h0lad/PicoLoRaHarvester/src/LoRaWAN/App/lora_app.c

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

/* Includes ------------------------------------------------------------------*/
#include "platform.h"
#include "sys_app.h"
#include "lora_app.h"
#include "stm32_seq.h"
#include "stm32_timer.h"
#include "utilities_def.h"
#include "app_version.h"
#include "Commissioning.h"
#include "subghz_phy_version.h"
#include "smtc_modem_api.h"
#include "smtc_modem_utilities.h"
#include "smtc_modem_hal.h"
#include "smtc_modem_relay_api.h"
#include "adc_if.h"
#include "CayenneLpp.h"
#include "sys_sensors.h"
#include "flash_if.h"
#include "rng.h"
#include "lorawan_api.h"
#include "stm32_lpm.h"

/* USER CODE BEGIN Includes */
#include "telemetry.h"
#include <stdlib.h>
/* USER CODE END Includes */

/* External variables ---------------------------------------------------------*/
/**
  * @brief LoRa State Machine states
  */
typedef enum TxEventType_e
{
  /**
    * @brief Appdata Transmission issue based on timer every TxDutyCycleTime
    */
  TX_ON_TIMER,
  /**
    * @brief Appdata Transmission external event plugged on OnSendEvent( )
    */
  TX_ON_EVENT
} TxEventType_t;

/**
  * LEDs period value of the timer in ms
  */
#define LED_PERIOD_TIME 500

/**
  * Join switch period value of the timer in ms
  */
#define JOIN_TIME 2000

/**
  * Uplink time interval in Certification mode is 10s (recommended value)
  */
#define CERT_TX_DUTYCYCLE   10

/**
  * Stack id value (multistacks modem is not yet available)
  */
#define STACK_ID 0

/*---------------------------------------------------------------------------*/
/*                             LoRaWAN NVM configuration                     */
/*---------------------------------------------------------------------------*/
/**
  * @brief LoRaWAN NVM Flash address
  * @note last 2 sector of a 256kBytes device
  */
#define LORAWAN_NVM_BASE_ADDRESS        (0x0803F000UL)

#define SECURE_ELEMENT_CONTEXT_SIZE     0x2A0UL
#define MODEM_CONTEXT_SIZE              0x10UL
#define LORAWAN_CONTEXT_SIZE            0x28UL

#define ADDR_FLASH_LORAWAN_CONTEXT              LORAWAN_NVM_BASE_ADDRESS
#define ADDR_FLASH_MODEM_CONTEXT                (void *)(LORAWAN_NVM_BASE_ADDRESS + LORAWAN_CONTEXT_SIZE)
#define ADDR_FLASH_SECURE_ELEMENT_CONTEXT       (void *)(LORAWAN_NVM_BASE_ADDRESS + LORAWAN_CONTEXT_SIZE + MODEM_CONTEXT_SIZE)

/* USER CODE BEGIN PD */
#define TTN_MAX_DAILY_AIRTIME_S       30UL
#define SECONDS_PER_DAY               86400UL
#define TTN_AIRTIME_USAGE_PCT         100UL
#define TX_INTERVAL_MIN_S             60UL
#define LORAWAN_MAC_OVERHEAD_BYTES    13UL
#define DOWNLINK_CMD_UPLINK           0x01U
#define DOWNLINK_CMD_RESET            0x02U
/* USER CODE END PD */


/*!
 * @brief Stringify constants
 */
#define xstr( a ) str( a )
#define str( a ) #a

/*!
 * @brief Helper macro that returned a human-friendly message if a command does not return SMTC_MODEM_RC_OK
 *
 * @remark The macro is implemented to be used with functions returning a @ref smtc_modem_return_code_t
 *
 * @param[in] rc  Return code
 */

#define ASSERT_SMTC_MODEM_RC( rc_func )                                                     \
  do                                                                                        \
  {                                                                                         \
    smtc_modem_return_code_t rc = rc_func;                                                  \
    if( rc == SMTC_MODEM_RC_NOT_INIT )                                                      \
    {                                                                                       \
      APP_LOG(TS_OFF, VLEVEL_H,  "In %s - %s (line %d): %s\r\n", __FILE__, __func__, __LINE__,   \
              xstr( SMTC_MODEM_RC_NOT_INIT ) );                             \
    }                                                                                       \
    else if( rc == SMTC_MODEM_RC_INVALID )                                                  \
    {                                                                                       \
      APP_LOG(TS_OFF, VLEVEL_H,  "In %s - %s (line %d): %s\r\n", __FILE__, __func__, __LINE__,   \
              xstr( SMTC_MODEM_RC_INVALID ) );                              \
    }                                                                                       \
    else if( rc == SMTC_MODEM_RC_BUSY )                                                     \
    {                                                                                       \
      APP_LOG(TS_OFF, VLEVEL_H,  "In %s - %s (line %d): %s\r\n", __FILE__, __func__, __LINE__,   \
              xstr( SMTC_MODEM_RC_BUSY ) );                                 \
    }                                                                                       \
    else if( rc == SMTC_MODEM_RC_FAIL )                                                     \
    {                                                                                       \
      APP_LOG(TS_OFF, VLEVEL_H,  "In %s - %s (line %d): %s\r\n", __FILE__, __func__, __LINE__,   \
              xstr( SMTC_MODEM_RC_FAIL ) );                                 \
    }                                                                                       \
    else if( rc == SMTC_MODEM_RC_NO_TIME )                                                  \
    {                                                                                       \
      APP_LOG(TS_OFF, VLEVEL_L,  "In %s - %s (line %d): %s\r\n", __FILE__, __func__, __LINE__, \
              xstr( SMTC_MODEM_RC_NO_TIME ) );                            \
    }                                                                                       \
    else if( rc == SMTC_MODEM_RC_INVALID_STACK_ID )                                         \
    {                                                                                       \
      APP_LOG(TS_OFF, VLEVEL_H,  "In %s - %s (line %d): %s\r\n", __FILE__, __func__, __LINE__,   \
              xstr( SMTC_MODEM_RC_INVALID_STACK_ID ) );                     \
    }                                                                                       \
    else if( rc == SMTC_MODEM_RC_NO_EVENT )                                                 \
    {                                                                                       \
      APP_LOG(TS_OFF, VLEVEL_M,  "In %s - %s (line %d): %s\r\n", __FILE__, __func__, __LINE__,    \
              xstr( SMTC_MODEM_RC_NO_EVENT ) );                              \
    }                                                                                       \
  } while( 0 )


/**
  * @brief  LoRa End Node send request
  */
static void SendTxData(uint8_t port);
#if defined (LOW_POWER_DISABLE) && (LOW_POWER_DISABLE == 0)
/**
  * @brief  Sleep timer callback function
  * @param  context ptr
  */
static void OnSleepTimerEvent(void *context);
#endif /* (LOW_POWER_DISABLE) && (LOW_POWER_DISABLE == 0) */

/**
  * @brief User callback for event
  *
  *  This callback is called every time an event ( see smtc_modem_event_t ) appears in the modem.
  *  Several events may have to be read from the modem when this callback is called.
  */
static void EventCallback(void);

/*!
 * Restore the NVM Data context from the Flash
 *
* @param [in]  ctx_type   Type of modem context that need to be restored
* @param [in]  offset     Memory offset after ctx_type address
* @param [out] buffer     Buffer pointer to write to
* @param [in]  size       Buffer size to read in bytes
*/
static void RestoreContext(const modem_context_type_t ctx_type, uint32_t offset, uint8_t *buffer, const uint32_t size);
/*!
 * Store the NVM Data context to the Flash
 *
* @param [in] ctx_type   Type of modem context that need to be saved
* @param [in] offset     Memory offset after ctx_type address
* @param [in] buffer     Buffer pointer to write from
* @param [in] size       Buffer size to write in bytes
*/
static void StoreContext(const modem_context_type_t ctx_type, uint32_t offset, const uint8_t *buffer,
                         const uint32_t size);
/*!
 * Get Random value using the RNG module
 *
 * \retval value  Return the random value
 */
static uint32_t GetRandomValue(void);

/*!
 * Will be called to reset the system
 * \note Compliance test protocol callbacks used when TS001-1.0.4 + TS009 1.0.0 are defined
 */
static void SystemReset(void);

/* USER CODE BEGIN PFP */
static uint32_t compute_toa_ms(uint8_t dr, uint8_t payload_len);
static uint32_t compute_tx_interval_s(uint8_t dr);
/* USER CODE END PFP */


/**
  * @brief LoRaWAN User credentials
  */
static uint8_t user_dev_eui[8]      = FORMAT32_KEY(LORAWAN_DEVICE_EUI);
static uint8_t user_join_eui[8]     = FORMAT32_KEY(LORAWAN_JOIN_EUI);
static uint8_t user_gen_app_key[16] = FORMAT_KEY(LORAWAN_GEN_APP_KEY);
static uint8_t user_app_key[16]     = FORMAT_KEY(LORAWAN_APP_KEY);
/**
  * @brief  Buffer for rx payload
  */
static uint8_t                  rx_payload[SMTC_MODEM_MAX_LORAWAN_PAYLOAD_LENGTH] = { 0 };

/**
  * @brief  Size of the payload in the rx_payload buffer
  */
static uint8_t                  rx_payload_size = 0;

/**
  * @brief  Metadata of downlink
  */
static smtc_modem_dl_metadata_t rx_metadata     = { 0 };

/**
  * @brief  Remaining downlink payload in modem
  */
static uint8_t                  rx_remaining    = 0;

/**
  * @brief  Flag for button status
  */
static volatile bool user_button_is_press = false;

/**
  * @brief LoRaWAN Certification Mode
  */
static bool CertMode = LORAWAN_CERTIFICATION_MODE;

/**
  * @brief Type of Event to generate application Tx
  */
static TxEventType_t EventType = TX_ON_TIMER;

#if defined (LOW_POWER_DISABLE) && (LOW_POWER_DISABLE == 0)
/**
  * @brief Timer to handle the sleep time
  */
static UTIL_TIMER_Object_t SleepTimer;
#endif /* (LOW_POWER_DISABLE) && (LOW_POWER_DISABLE == 0) */

/**
  * Temp buffer to store a FLASH page in RAM when partial replacement is needed
  */
static uint8_t FLASH_RAM_buffer[FLASH_IF_BUFFER_SIZE];

/**
  * @brief Handler Callbacks
  */
static Callbacks_t Callbacks =
{
  .EventCallback =                EventCallback,
  .RestoreContext =               RestoreContext,
  .StoreContext =                 StoreContext,
  .GetRandomValue =               GetRandomValue,
  .GetBatteryLevel =              GetBatteryLevel,
  .GetTemperatureLevel =          GetTemperatureLevel,
  .SystemReset =                  SystemReset,
};

/* USER CODE BEGIN PV */
/**
  * @brief User application payload buffer
  */
static uint8_t AppDataBuffer[LORAWAN_APP_DATA_BUFFER_MAX_SIZE];
/* USER CODE END PV */

/* Exported functions ---------------------------------------------------------*/
/*
 * -----------------------------------------------------------------------------
 * --- PUBLIC FUNCTIONS DEFINITION ---------------------------------------------
 */

void LoRaWAN_Init(void)
{
  /* USER CODE BEGIN LoRaWAN_Init_1 */
  telemetry_init();
  /* USER CODE END LoRaWAN_Init_1 */

  if (FLASH_IF_Init(FLASH_RAM_buffer) != FLASH_IF_OK)
  {
    Error_Handler();
  }

#if defined (LOW_POWER_DISABLE) && (LOW_POWER_DISABLE == 0)
  UTIL_TIMER_Create(&SleepTimer, LED_PERIOD_TIME, UTIL_TIMER_ONESHOT, OnSleepTimerEvent, NULL);
#endif /* (LOW_POWER_DISABLE) && (LOW_POWER_DISABLE == 0) */
  /* Init the Lora Stack*/
  /* Init the modem and use EventCallback as event callback, please note that the callback will be */
  /* called immediately after the first call to smtc_modem_run_engine because of the reset detection */
  smtc_modem_init(&Callbacks);

  /* Certification mode is disabled by default. It can be enabled setting LORAWAN_CERTIFICATION_MODE to true */
  smtc_modem_set_certification_mode(STACK_ID, CertMode);

  /* BSP crystal accurrancy could be set to a different value. By default it is 10. */
  smtc_modem_set_crystal_error_ppm(BSP_CRYSTAL_ERROR);

}

void LoRaWAN_Process(void)
{
  uint32_t sleep_time_ms = 0;

  /* Sample sensors (voltage/current every 30 s, temp/humidity/mcu every 5 min) */
  telemetry_process();

  /* Check button */
  if (user_button_is_press == true)
  {
    user_button_is_press = false;

    smtc_modem_status_mask_t status_mask = 0;
    smtc_modem_get_status(STACK_ID, &status_mask);
    /* Check if the device has already joined a network */
    if ((status_mask & SMTC_MODEM_STATUS_JOINED) == SMTC_MODEM_STATUS_JOINED)
    {
      /* Send packet */
      SendTxData(LORAWAN_USER_APP_PORT);
    }
  }

  /* Modem process launch */
  sleep_time_ms = smtc_modem_run_engine();

  /* Cap the sleep so the next sensor sample wakes the MCU on time */
  {
    uint32_t sample_cap_ms = telemetry_sleep_cap_ms();
    if ((sample_cap_ms == 0) || (sample_cap_ms < sleep_time_ms))
    {
      sleep_time_ms = sample_cap_ms;
    }
  }

  /* Atomically check sleep conditions (button was not pressed and no modem flags pending) */

  if ((user_button_is_press == false) && (smtc_modem_is_irq_flag_pending() == false))
  {
    if (sleep_time_ms > 0)
    {
#if defined (LOW_POWER_DISABLE) && (LOW_POWER_DISABLE == 0)
      UTIL_TIMER_SetPeriod(&SleepTimer, sleep_time_ms);
      UTIL_TIMER_Start(&SleepTimer);
      UTIL_LPM_EnterLowPower();
#endif
    }
  }

}

static void SystemReset(void)
{
  __disable_irq();
  HAL_NVIC_SystemReset();   /* Restart system */
}

static uint32_t GetRandomValue(void)
{
  uint32_t rand_nb = 0;

  /* RNG initialized once by MX_RNG_Init(); avoid re-init timeout. */
  if (HAL_RNG_GenerateRandomNumber(&hrng, &rand_nb) != HAL_OK)
  {
    Error_Handler();
  }

  return rand_nb;
}

static void RestoreContext(const modem_context_type_t ctx_type, uint32_t offset, uint8_t *buffer,
                           const uint32_t size)
{
  /* Offset is only used for fuota and store and forward purpose and for multistack features. To avoid ram consumption */
  /* the use of hal_flash_read_modify_write is only done in these cases */
  FLASH_IF_StatusTypedef ret_status = FLASH_IF_OK;
  switch (ctx_type)
  {
    case CONTEXT_MODEM:
      ret_status = FLASH_IF_Read(buffer, ADDR_FLASH_MODEM_CONTEXT, MODEM_CONTEXT_SIZE);
      break;
    case CONTEXT_LORAWAN_STACK:
      ret_status = FLASH_IF_Read(buffer, (void *)((uint32_t)(ADDR_FLASH_LORAWAN_CONTEXT + offset)), LORAWAN_CONTEXT_SIZE);
      break;
    case CONTEXT_SECURE_ELEMENT:
      ret_status = FLASH_IF_Read(buffer, ADDR_FLASH_SECURE_ELEMENT_CONTEXT, SECURE_ELEMENT_CONTEXT_SIZE);
      break;
    default:
      break;
  }
  if (ret_status != 0)
  {
    APP_LOG(TS_OFF, VLEVEL_M, "restore ctx type %d, FLASH_IF return: %d\r\n", ctx_type, ret_status);
  }
}

static void StoreContext(const modem_context_type_t ctx_type, uint32_t offset, const uint8_t *buffer,
                         const uint32_t size)
{
  FLASH_IF_StatusTypedef ret_status = FLASH_IF_OK;
  /* Offset is only used for fuota and store and forward purpose and for multistack features. To avoid ram consumption
   * the use of hal_flash_read_modify_write is only done in these cases */
  switch (ctx_type)
  {
    case CONTEXT_MODEM:
    {
      ret_status = FLASH_IF_Write(ADDR_FLASH_MODEM_CONTEXT, (const void *)buffer, MODEM_CONTEXT_SIZE);
    }

    break;
    case CONTEXT_LORAWAN_STACK:
    {
      ret_status = FLASH_IF_Write((void *)((uint32_t)(ADDR_FLASH_LORAWAN_CONTEXT + offset)), (const void *)buffer, (uint32_t)LORAWAN_CONTEXT_SIZE);
    }
    break;
    case CONTEXT_SECURE_ELEMENT:
    {
      ret_status = FLASH_IF_Write(ADDR_FLASH_SECURE_ELEMENT_CONTEXT, (const void *)buffer, SECURE_ELEMENT_CONTEXT_SIZE);
    }
    break;

    default:
      break;
  }
  if (ret_status != 0)
  {
    APP_LOG(TS_OFF, VLEVEL_M, "store ctx type %d, FLASH_IF return: %d\r\n", ctx_type, ret_status);
  }
}

static void EventCallback(void)
{
  smtc_modem_event_t current_event;
  uint8_t            event_pending_count;
  uint8_t            stack_id = STACK_ID;
  smtc_modem_status_mask_t status_mask = 0;

  /* Continue to read modem event until all event has been processed */
  do
  {
    /* Read modem event */
    ASSERT_SMTC_MODEM_RC(smtc_modem_get_event(&current_event, &event_pending_count));

    switch (current_event.event_type)
    {
      case SMTC_MODEM_EVENT_RESET:
        APP_LOG(TS_OFF, VLEVEL_M, "Event received: RESET\r\n");

        /* Set user credentials */
        ASSERT_SMTC_MODEM_RC(smtc_modem_set_deveui(stack_id, user_dev_eui));
        ASSERT_SMTC_MODEM_RC(smtc_modem_set_joineui(stack_id, user_join_eui));
        ASSERT_SMTC_MODEM_RC(smtc_modem_set_appkey(stack_id, user_gen_app_key));
        ASSERT_SMTC_MODEM_RC(smtc_modem_set_nwkkey(stack_id, user_app_key));

        /* Set user region */
        ASSERT_SMTC_MODEM_RC(smtc_modem_set_region(stack_id, ACTIVE_REGION));

        ASSERT_SMTC_MODEM_RC(smtc_modem_set_join_duty_cycle_backoff_bypass(stack_id, false));

        /* Print Security material */
        SecureElementPrintKeys(stack_id);
        CertMode = (smtc_modem_is_certification_port_disabled(STACK_ID)) ? 0 : CertMode;
        if (CertMode == false)
        {
          /* Schedule a Join LoRaWAN network */
          ASSERT_SMTC_MODEM_RC(smtc_modem_join_network(stack_id));
        }
        break;

      case SMTC_MODEM_EVENT_ALARM:
        APP_LOG(TS_OFF, VLEVEL_M,  "Event received: ALARM\r\n");
        if (CertMode == true)
        {
          ASSERT_SMTC_MODEM_RC(smtc_modem_alarm_clear_timer());
        }
        else
        {
          /* Send periodical uplink */
          SendTxData(LORAWAN_USER_APP_PORT);
        }
        break;

      case SMTC_MODEM_EVENT_JOINED:
        APP_LOG(TS_OFF, VLEVEL_M,  "Event received: JOINED\r\n");
        APP_LOG(TS_OFF, VLEVEL_H,  "Modem is now joined \r\n");
        if (CertMode == false)
        {
#if ( LORAMAC_CLASSB_ENABLED == 1 )
          smtc_modem_set_class(stack_id, SMTC_MODEM_CLASS_B);
#endif
          /* Send first periodical uplink */
          SendTxData(LORAWAN_USER_APP_PORT);
        }
        break;

      case SMTC_MODEM_EVENT_TXDONE:
        APP_LOG(TS_OFF, VLEVEL_M,  "Event received: TXDONE\r\n");
        APP_LOG(TS_OFF, VLEVEL_H,  "Transmission done \r\n");
        smtc_modem_get_status(STACK_ID, &status_mask);
        break;

      case SMTC_MODEM_EVENT_DOWNDATA:
        APP_LOG(TS_OFF, VLEVEL_M,  "Event received: DOWNDATA\r\n");
        /* Get downlink data */
        ASSERT_SMTC_MODEM_RC(smtc_modem_get_downlink_data(rx_payload, &rx_payload_size, &rx_metadata, &rx_remaining));
        APP_LOG(TS_OFF, VLEVEL_M, "Data received on port %u\r\n", rx_metadata.fport);
        /* APP_LOG(TS_OFF, VLEVEL_M, "Received payload", rx_payload, rx_payload_size ); */

        /* Handle application downlink commands. */
        if ((rx_metadata.fport == LORAWAN_USER_APP_PORT) && (rx_payload_size >= 1))
        {
          switch (rx_payload[0])
          {
            case DOWNLINK_CMD_UPLINK:
              APP_LOG(TS_OFF, VLEVEL_M, "downlink cmd: immediate uplink\r\n");
              SendTxData(LORAWAN_USER_APP_PORT);
              break;
            case DOWNLINK_CMD_RESET:
              APP_LOG(TS_OFF, VLEVEL_M, "downlink cmd: reset\r\n");
              SystemReset();
              break;
            default:
              APP_LOG(TS_OFF, VLEVEL_M, "downlink cmd: unknown 0x%02X\r\n", rx_payload[0]);
              break;
          }
        }
        break;

      case SMTC_MODEM_EVENT_JOINFAIL:
        APP_LOG(TS_OFF, VLEVEL_M,  "Event received: JOINFAIL\r\n");
        smtc_modem_get_status(STACK_ID, &status_mask);
        break;

      case SMTC_MODEM_EVENT_ALCSYNC_TIME:
        APP_LOG(TS_OFF, VLEVEL_M,  "Event received: ALCSync service TIME\r\n");
        break;

      case SMTC_MODEM_EVENT_LINK_CHECK:
        APP_LOG(TS_OFF, VLEVEL_M,  "Event received: LINK_CHECK\r\n");
        break;

      case SMTC_MODEM_EVENT_CLASS_B_PING_SLOT_INFO:
        APP_LOG(TS_OFF, VLEVEL_M,  "Event received: CLASS_B_PING_SLOT_INFO\r\n");
        break;

      case SMTC_MODEM_EVENT_CLASS_B_STATUS:
        APP_LOG(TS_OFF, VLEVEL_M,  "Event received: CLASS_B_STATUS\r\n");
        break;

      case SMTC_MODEM_EVENT_LORAWAN_MAC_TIME:
        APP_LOG(TS_OFF, VLEVEL_L,  "Event received: LORAWAN MAC TIME\r\n");
        break;

      case SMTC_MODEM_EVENT_LORAWAN_FUOTA_DONE:
      {
        bool status = current_event.event_data.fuota_status.successful;
        if (status == true)
        {
          APP_LOG(TS_OFF, VLEVEL_M,  "Event received: FUOTA SUCCESSFUL\r\n");
        }
        else
        {
          APP_LOG(TS_OFF, VLEVEL_L,  "Event received: FUOTA FAIL\r\n");
        }
        break;
      }

      case SMTC_MODEM_EVENT_NO_MORE_MULTICAST_SESSION_CLASS_C:
        APP_LOG(TS_OFF, VLEVEL_M,  "Event received: MULTICAST CLASS_C STOP\r\n");
        break;

      case SMTC_MODEM_EVENT_NO_MORE_MULTICAST_SESSION_CLASS_B:
        APP_LOG(TS_OFF, VLEVEL_M,  "Event received: MULTICAST CLASS_B STOP\r\n");
        break;

      case SMTC_MODEM_EVENT_NEW_MULTICAST_SESSION_CLASS_C:
        APP_LOG(TS_OFF, VLEVEL_M,  "Event received: New MULTICAST CLASS_C \r\n");
        break;

      case SMTC_MODEM_EVENT_NEW_MULTICAST_SESSION_CLASS_B:
        APP_LOG(TS_OFF, VLEVEL_M,  "Event received: New MULTICAST CLASS_B\r\n");
        break;

      case SMTC_MODEM_EVENT_FIRMWARE_MANAGEMENT:
        APP_LOG(TS_OFF, VLEVEL_M,  "Event received: FIRMWARE_MANAGEMENT\r\n");
        if (current_event.event_data.fmp.status == SMTC_MODEM_EVENT_FMP_REBOOT_IMMEDIATELY)
        {
          HAL_NVIC_SystemReset();
        }
        break;

      case SMTC_MODEM_EVENT_STREAM_DONE:
        APP_LOG(TS_OFF, VLEVEL_M,  "Event received: STREAM_DONE\r\n");
        break;

      case SMTC_MODEM_EVENT_UPLOAD_DONE:
        APP_LOG(TS_OFF, VLEVEL_M,  "Event received: UPLOAD_DONE\r\n");
        break;

      case SMTC_MODEM_EVENT_DM_SET_CONF:
        APP_LOG(TS_OFF, VLEVEL_M,  "Event received: DM_SET_CONF\r\n");
        break;

      case SMTC_MODEM_EVENT_MUTE:
        APP_LOG(TS_OFF, VLEVEL_M,  "Event received: MUTE\r\n");
        break;
      case SMTC_MODEM_EVENT_REGIONAL_DUTY_CYCLE:
      {
        uint8_t duty_cycle_status = current_event.event_data.regional_duty_cycle.status;
        APP_LOG(TS_OFF, VLEVEL_M,  "Event received: DUTY_CYCLE busy %d\r\n", duty_cycle_status);
      }
      break;
      default:
        APP_LOG(TS_OFF, VLEVEL_M,  "Unknown event %u\r\n", current_event.event_type);
        break;
    }
  } while (event_pending_count > 0);
}

static void RestartUplinkAlarm(uint32_t interval_s)
{
  if (EventType != TX_ON_TIMER)
  {
    return;
  }

  smtc_modem_status_mask_t status_mask = 0;
  smtc_modem_get_status(STACK_ID, &status_mask);
  if (CertMode || ((status_mask & SMTC_MODEM_STATUS_JOINED) != SMTC_MODEM_STATUS_JOINED))
  {
    ASSERT_SMTC_MODEM_RC(smtc_modem_alarm_start_timer(CERT_TX_DUTYCYCLE));
  }
  else
  {
    int32_t dtc_ms = 0;
    smtc_modem_get_duty_cycle_status(STACK_ID, &dtc_ms);
    if (dtc_ms < 0)
    {
      uint32_t dtc_s = (uint32_t)(((uint32_t)(-dtc_ms) + 999UL) / 1000UL);
      if (dtc_s > interval_s)
      {
        interval_s = dtc_s;
      }
    }
    ASSERT_SMTC_MODEM_RC(smtc_modem_alarm_start_timer(interval_s));
  }
}

static void SendTxData(uint8_t port)
{
  /* USER CODE BEGIN SendTxData_1 */
  telemetry_data_t telemetry = {0};
  uint8_t bufferSize = 0;

  if (!telemetry_collect(&telemetry))
  {
    APP_LOG(TS_OFF, VLEVEL_M, "No valid telemetry data yet, skip uplink\r\n");
    RestartUplinkAlarm(TX_INTERVAL_MIN_S);
    return;
  }

  bufferSize = telemetry_encode(&telemetry, AppDataBuffer);

  APP_LOG(TS_OFF, VLEVEL_M, "sensors cur %u/%u/%u uA  vbat %u/%u/%u mV\r\n",
          telemetry.current_min_ua, telemetry.current_avg_ua, telemetry.current_max_ua,
          telemetry.voltage_min_mv, telemetry.voltage_avg_mv, telemetry.voltage_max_mv);
  APP_LOG(TS_OFF, VLEVEL_M, "sensors temp %d.%d C  hum %u.%u %%  mcu %d.%d C\r\n",
          telemetry.temperature_avg / 10, abs(telemetry.temperature_avg % 10),
          telemetry.humidity_avg / 10, telemetry.humidity_avg % 10,
          telemetry.mcu_temperature / 10, abs(telemetry.mcu_temperature % 10));

  ASSERT_SMTC_MODEM_RC(smtc_modem_request_uplink(STACK_ID, port, false, AppDataBuffer, bufferSize));

  /* Restart the periodical uplink alarm */
  RestartUplinkAlarm(compute_tx_interval_s(lorawan_api_next_dr_get(STACK_ID)));

  /* USER CODE END SendTxData_1 */
}

/* USER CODE BEGIN PrFD_LedEvents */
static uint32_t compute_toa_ms(uint8_t dr, uint8_t payload_len)
{
  uint32_t sf;
  uint32_t bw_hz;
  uint32_t symbol_us;
  uint32_t preamble_us;
  uint32_t num;
  uint32_t den;
  uint32_t de;
  uint32_t total_us;

  if (dr > 6)
  {
    dr = 6;
  }

  switch (dr)
  {
    case 0:
      sf = 12;
      bw_hz = 125000UL;
      break;
    case 1:
      sf = 11;
      bw_hz = 125000UL;
      break;
    case 2:
      sf = 10;
      bw_hz = 125000UL;
      break;
    case 3:
      sf = 9;
      bw_hz = 125000UL;
      break;
    case 4:
      sf = 8;
      bw_hz = 125000UL;
      break;
    case 5:
      sf = 7;
      bw_hz = 125000UL;
      break;
    default:
      sf = 7;
      bw_hz = 250000UL;
      break;
  }

  symbol_us = ((1UL << sf) * 1000000UL) / bw_hz;
  preamble_us = (49UL * symbol_us) / 4UL;
  de = (sf >= 11) ? 1UL : 0UL;

  num = 8UL * payload_len - 4UL * sf + 28UL + 16UL;
  den = 4UL * (sf - 2UL * de);
  total_us = preamble_us + (8UL + ((num + den - 1UL) / den) * 5UL) * symbol_us;

  return (total_us + 999UL) / 1000UL;
}

static uint32_t compute_tx_interval_s(uint8_t dr)
{
  uint32_t toa_ms = compute_toa_ms(dr, TELEMETRY_PAYLOAD_SIZE + LORAWAN_MAC_OVERHEAD_BYTES);
  uint32_t interval_s = (uint32_t)(((uint64_t)toa_ms * SECONDS_PER_DAY * 100UL) /
                                   (TTN_MAX_DAILY_AIRTIME_S * 1000UL * TTN_AIRTIME_USAGE_PCT));

  if (interval_s < TX_INTERVAL_MIN_S)
  {
    interval_s = TX_INTERVAL_MIN_S;
  }
  return interval_s;
}
/* USER CODE END PrFD_LedEvents */

#if defined (LOW_POWER_DISABLE) && (LOW_POWER_DISABLE == 0)
static void OnSleepTimerEvent(void *context)
{
  APP_LOG(TS_ON, VLEVEL_H, "Sleep timer\r\n");

}
#endif /*(LOW_POWER_DISABLE) && (LOW_POWER_DISABLE == 0) */

/* --- EOF ------------------------------------------------------------------ */
