h0lad/PicoLoRaHarvester/src/Core/Src/stm32wlxx_it.c

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

/* Includes ------------------------------------------------------------------*/
#include "main.h"
#include "stm32wlxx_it.h"
/* USER CODE BEGIN 0 */
extern UART_HandleTypeDef huart2;
static void fault_dump(const char *tag)
{
  const char hex[] = "0123456789ABCDEF";
  uint32_t cfsr = *(volatile uint32_t *)0xE000ED28U;
  uint32_t hfsr = *(volatile uint32_t *)0xE000ED2CU;
  uint32_t pc   = *(volatile uint32_t *)(__get_MSP() + 24U);
  char msg[] = "  CFSR=00000000 HFSR=00000000 PC=00000000\r\n";
  int i;

  msg[0] = tag[0];
  msg[1] = tag[1];
  for (i = 0; i < 8; i++) msg[7 + 7 - i]  = hex[(cfsr >> (4 * i)) & 0xF];
  for (i = 0; i < 8; i++) msg[21 + 7 - i] = hex[(hfsr >> (4 * i)) & 0xF];
  for (i = 0; i < 8; i++) msg[33 + 7 - i] = hex[(pc >> (4 * i)) & 0xF];

  HAL_UART_Transmit(&huart2, (uint8_t *)msg, sizeof(msg) - 1, 1000);
  HAL_NVIC_SystemReset();
  while (1)
  {
  }
}
/* USER CODE END 0 */

/* External variables --------------------------------------------------------*/
extern RTC_HandleTypeDef hrtc;
extern UART_HandleTypeDef huart2;
extern SUBGHZ_HandleTypeDef hsubghz;

/******************************************************************************/
/*           Cortex Processor Interruption and Exception Handlers          */
/******************************************************************************/
/**
  * @brief This function handles Non maskable interrupt.
  */
void NMI_Handler(void)
{
  /* USER CODE BEGIN NonMaskableInt_IRQn 1 */
   while (1)
  {
  }
  /* USER CODE END NonMaskableInt_IRQn 1 */
}

/**
  * @brief This function handles Hard fault interrupt.
  */
void HardFault_Handler(void)
{
  /* USER CODE BEGIN HardFault_IRQn 0 */
  fault_dump("HF");
  /* USER CODE END HardFault_IRQn 0 */
  while (1)
  {
  }
}

/**
  * @brief This function handles Memory management fault.
  */
void MemManage_Handler(void)
{
  /* USER CODE BEGIN MemoryManagement_IRQn 0 */
  fault_dump("MF");
  /* USER CODE END MemoryManagement_IRQn 0 */
  while (1)
  {
  }
}

/**
  * @brief This function handles Prefetch fault, memory access fault.
  */
void BusFault_Handler(void)
{
  /* USER CODE BEGIN BusFault_IRQn 0 */
  fault_dump("BF");
  /* USER CODE END BusFault_IRQn 0 */
  while (1)
  {
  }
}

/**
  * @brief This function handles Undefined instruction or illegal state.
  */
void UsageFault_Handler(void)
{
  /* USER CODE BEGIN UsageFault_IRQn 0 */
  fault_dump("UF");
  /* USER CODE END UsageFault_IRQn 0 */
  while (1)
  {
  }
}

/**
  * @brief This function handles System service call via SWI instruction.
  */
void SVC_Handler(void)
{
}

/**
  * @brief This function handles Debug monitor.
  */
void DebugMon_Handler(void)
{
}

/**
  * @brief This function handles Pendable request for system service.
  */
void PendSV_Handler(void)
{
}

/**
  * @brief This function handles System tick timer.
  */
void SysTick_Handler(void)
{
  HAL_IncTick();
}

/******************************************************************************/
/* STM32WLxx Peripheral Interrupt Handlers                                    */
/* Add here the Interrupt Handlers for the used peripherals.                  */
/* For the available peripheral interrupt handler names,                      */
/* please refer to the startup file (startup_stm32wlxx.s).                    */
/******************************************************************************/

/**
  * @brief This function handles RTC Tamper, RTC TimeStamp, LSECSS and RTC SSRU Interrupts.
  */
void TAMP_STAMP_LSECSS_SSRU_IRQHandler(void)
{
  HAL_RTCEx_SSRUIRQHandler(&hrtc);
}

/**
  * @brief This function handles RTC Alarms (A and B) Interrupt.
  */
void RTC_Alarm_IRQHandler(void)
{
  HAL_RTC_AlarmIRQHandler(&hrtc);
}

/**
  * @brief This function handles USART2 Interrupt.
  */
void USART2_IRQHandler(void)
{
  HAL_UART_IRQHandler(&huart2);
}

/**
  * @brief This function handles SUBGHZ radio interrupt.
  */
void SUBGHZ_Radio_IRQHandler(void)
{
  HAL_SUBGHZ_IRQHandler(&hsubghz);
}
